ldocull/WR9R-Wifi-Enabled-Antenna-Selector/RS232_Upgrade/Software/AntennaSwitch232/test/WR9R_Antenna_Switch/SelectAnt1.py

import requests

url = "http://192.168.1.179/ONE"

response = requests.get(url)

if response.status_code == 200:
    print("Success!")
elif response.status_code == 404:
    print("Resource not found!")
else:
    print("Error!")

# print(response.text)
